logitiles/HEXBERRY-V-20Q100-0.9/HEXBERRY-V-20Q100.kicad_sch

## KiCad design HEXBERRY-V-20Q100.kicad_sch (2024-11-13)

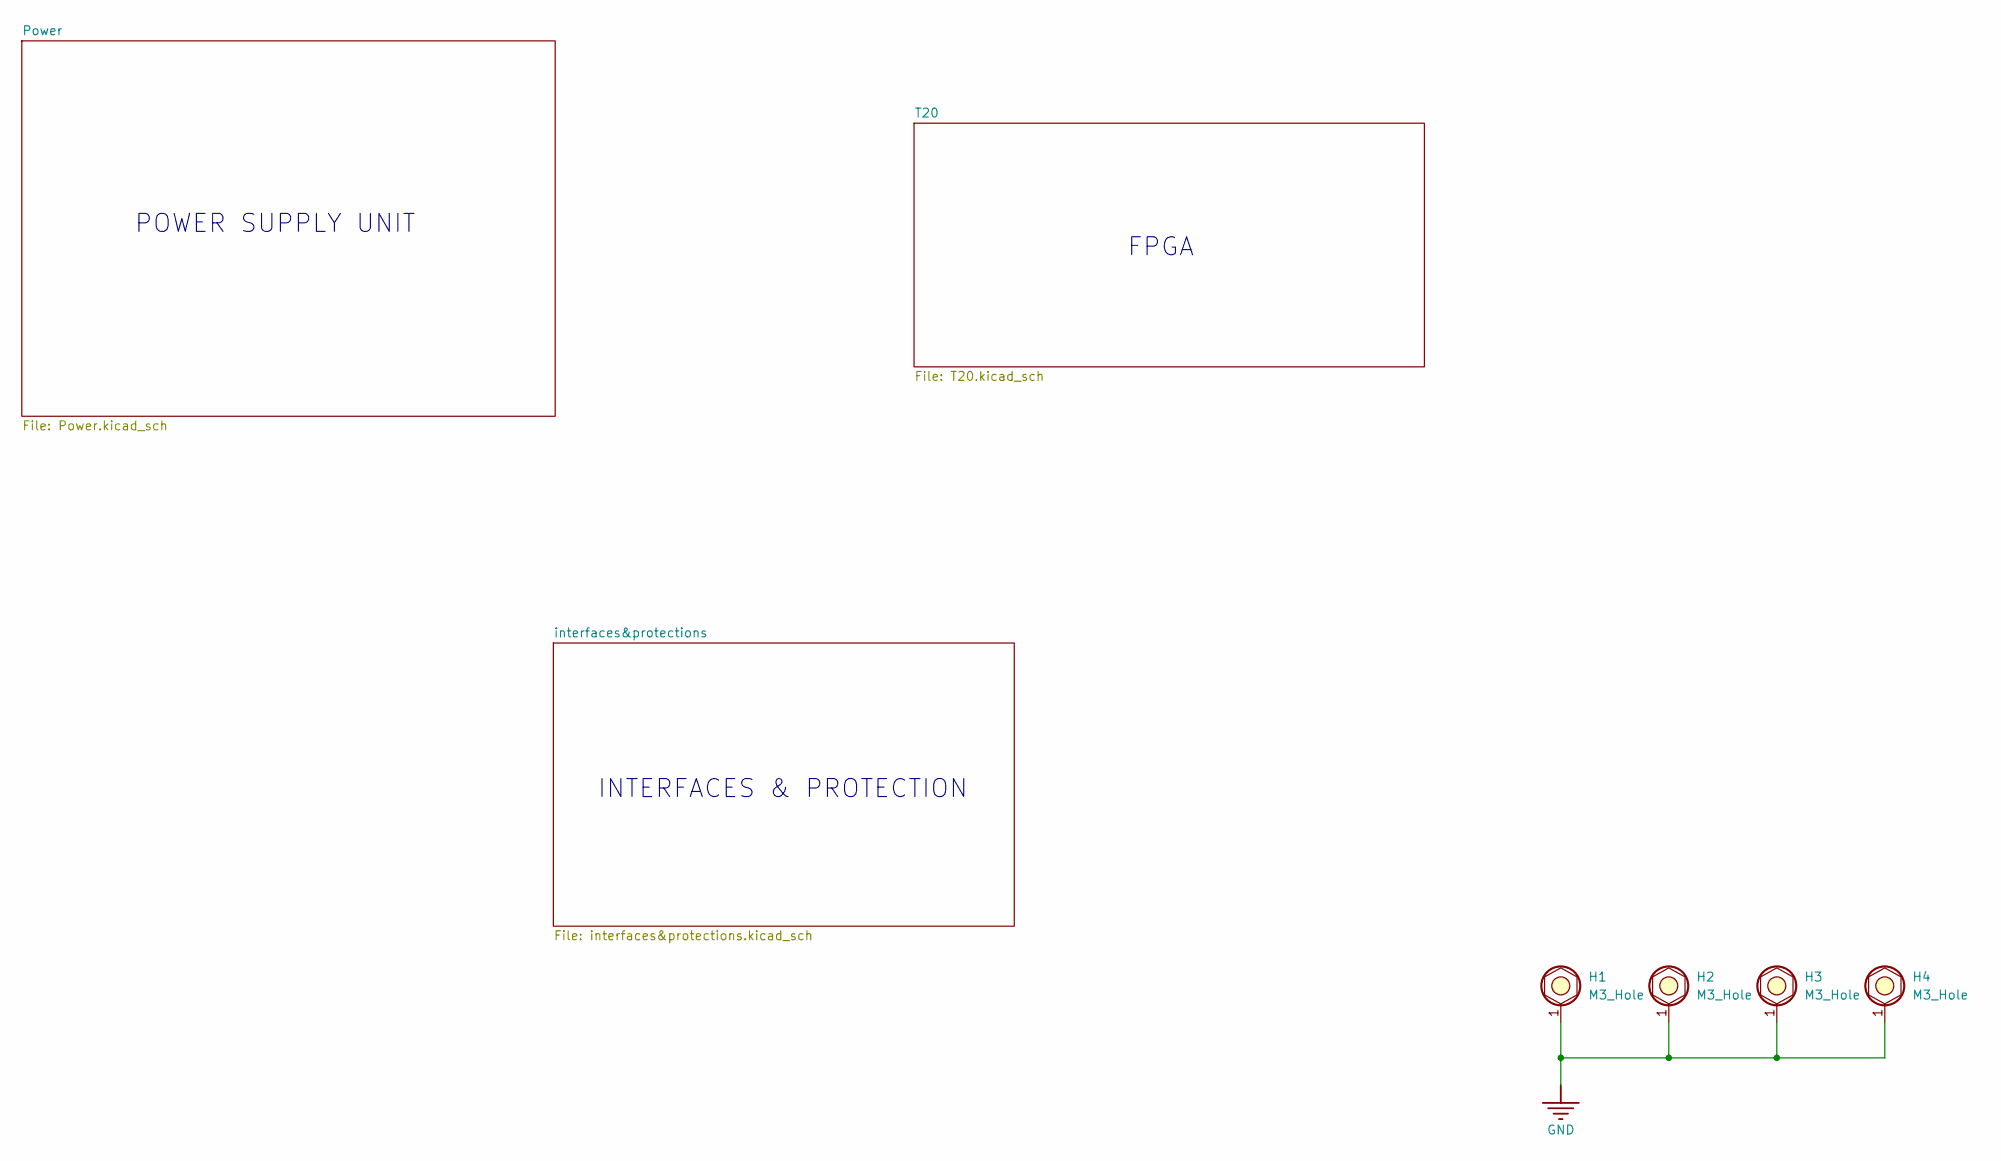
[picture p10: schematic HEXBERRY-V-20Q100.kicad_sch]

Parts:
H1, H2, H3, H4: M3_Hole; MountingHole_3.2mm_With_Spacer_H10mm

Connections:
GND: H1.1, H2.1, H3.1, H4.1

Notes on the sheet:
INTERFACES & PROTECTION
FPGA
POWER SUPPLY UNIT
