logitiles/HEXBERRY-V-20Q100-0.9/Power.kicad_sch

## KiCad design Power.kicad_sch (2024-11-13)

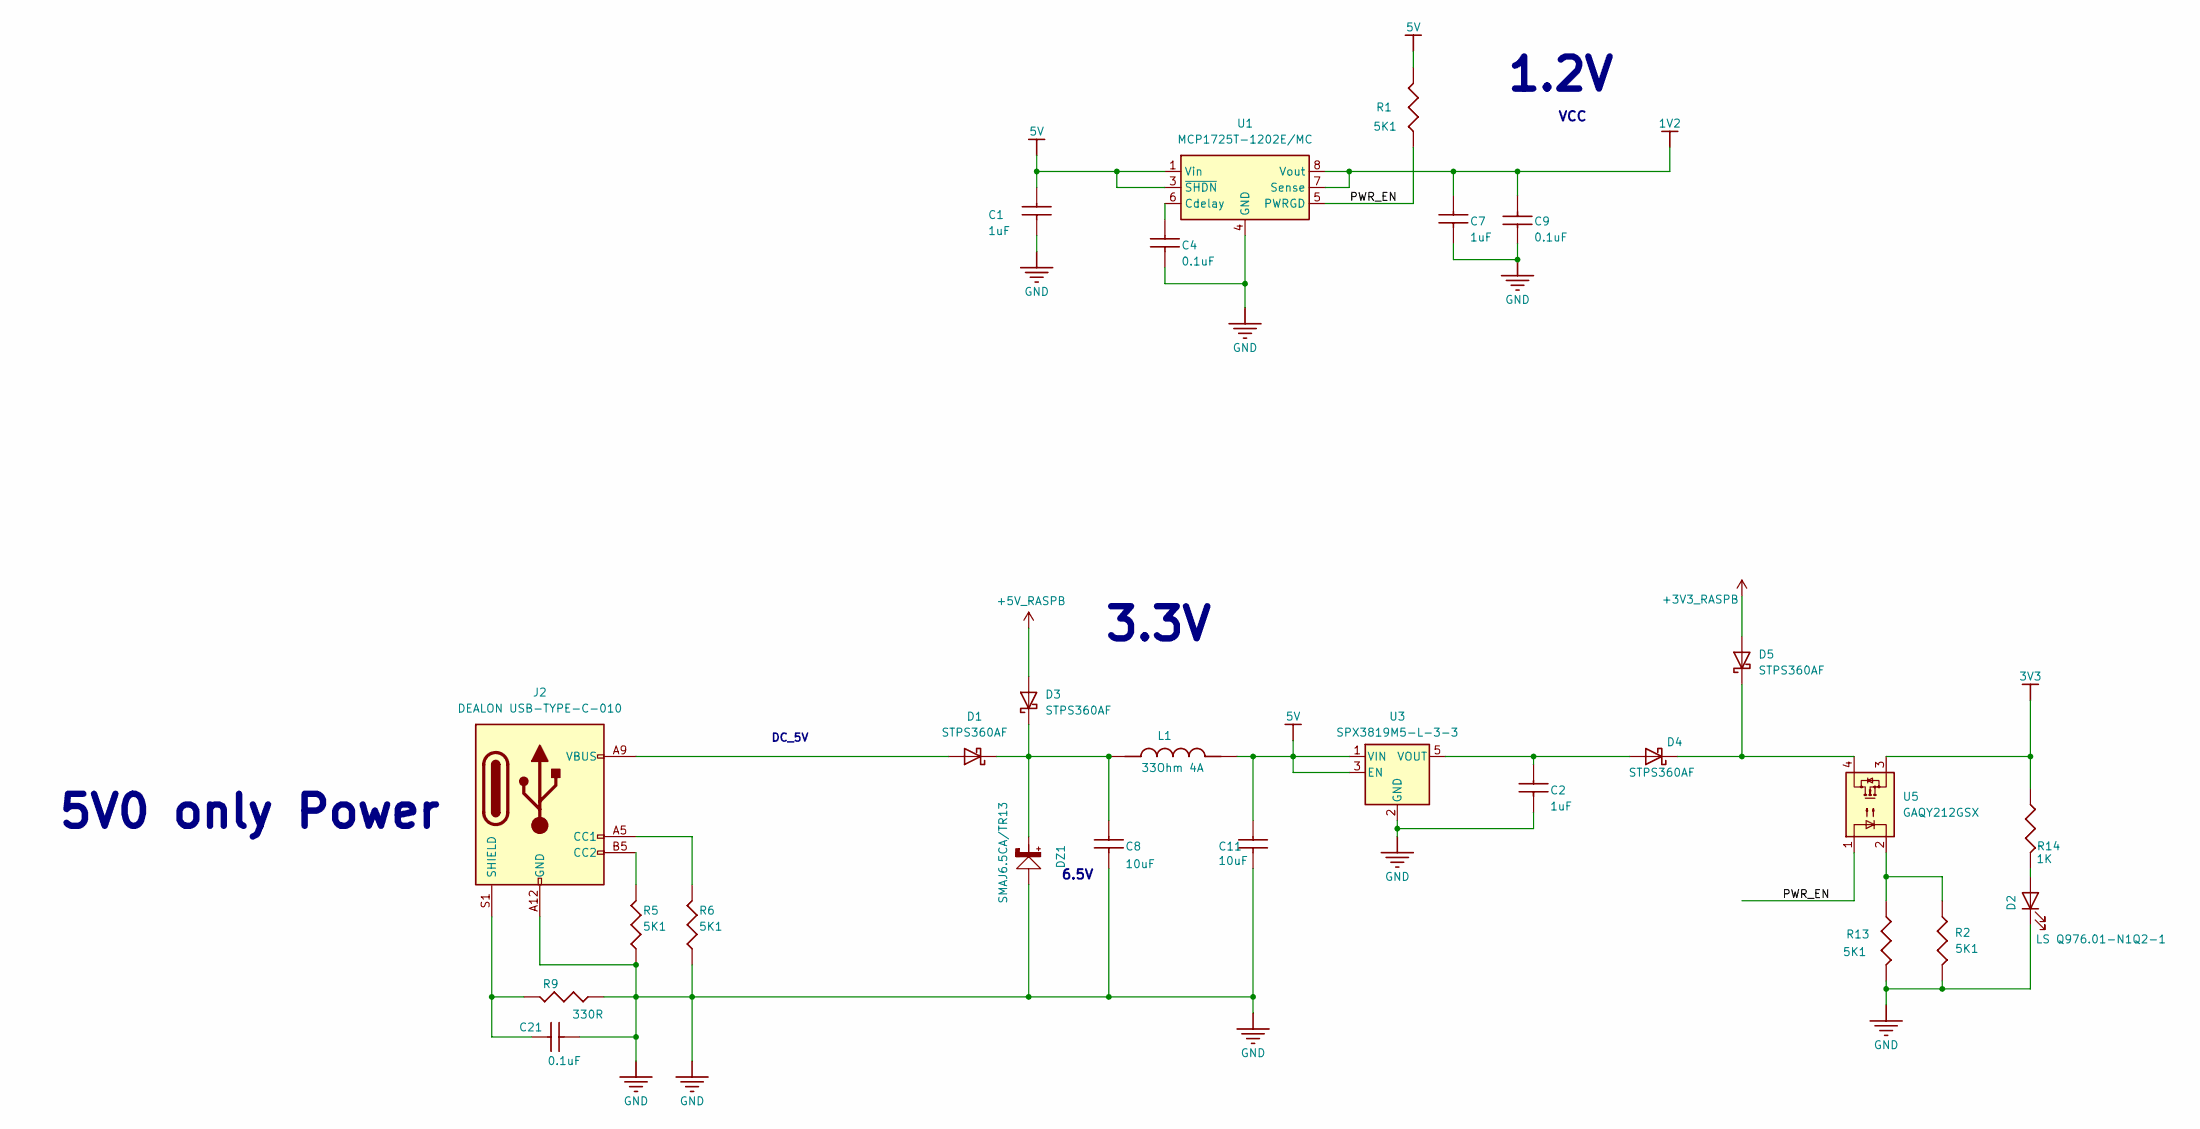
[picture p11: schematic Power.kicad_sch]

Parts:
C1, C2, C7: 1uF; C_0402_1005Metric
C4, C9, C21: 0.1uF; C_0402_1005Metric
C8, C11: 10uF; C_0603_1608Metric
D1, D3, D4, D5: STPS360AF; D_SOD-128
D2: LS Q976.01-N1Q2-1; LED_0603_1608Metric
DZ1: SMAJ6.5CA/TR13; D_SMA
J2: DEALON USB-TYPE-C-010; USB_C_Receptacle_GCT_USB4125-xx-x-0190_6P_TopMnt_Horizontal
L1: 33Ohm 4A; L_0603_1608Metric
R1, R2, R5, R6, R13: 5K1; R_0402_1005Metric
R9: 330R; R_0402_1005Metric
R14: 1K; R_0402_1005Metric
U1: MCP1725T-1202E/MC; DFN-8-1EP_3x3mm_P0.5mm_EP1.65x2.38mm_ThermalVias
U3: SPX3819M5-L-3-3; SOT-23-5
U5: GAQY212GSX; SOP-4_3.8x4.1mm_P2.54mm

Connections:
1V2: C7.1, C9.2, U1.7 (Sense), U1.8 (Vout)
3V3: R14.1, U5.3
5V: C1.1, C11.1, L1.1, R1.2, U1.1 (Vin), U1.2 (Vin), U1.3 (~SHDN), U3.1 (VIN), U3.3 (EN)
+3V3_RASPB: D5.2 (A)
+5V_RASPB: D3.2 (A)
GND: C1.2, C2.2, C4.2, C7.2, C8.2, C9.1, C11.2, C21.2, D2.1 (K), DZ1.1 (A), J2.A12 (GND), J2.B12 (GND), R2.2, R5.1, R6.1, R9.1, R13.2, U1.4 (GND), U1.9 (GND), U3.2 (GND)
unnamed: C2.1, D4.2 (A), U3.5 (VOUT)
unnamed: C4.1, U1.6 (Cdelay)
unnamed: C8.1, D1.1 (K), D3.1 (K), DZ1.2 (K), L1.2
unnamed: C21.1, J2.S1 (SHIELD), R9.2
unnamed: D1.2 (A), J2.A9 (VBUS), J2.B9 (VBUS)
unnamed: D2.2 (A), R14.2
unnamed: D4.1 (K), D5.1 (K), U5.4
unnamed: J2.A5 (CC1), R6.2
unnamed: J2.B5 (CC2), R5.2
unnamed: R2.1, R13.1, U5.2
PWR_EN: R1.1, U1.5 (PWRGD), U5.1

Notes on the sheet:
6.5V
DC_5V
3.3V
1.2V
5V0 only Power
VCC
