logitiles/HEXBERRY-V-20Q100-0.9/T20.kicad_sch

## KiCad design T20.kicad_sch (2024-11-13)

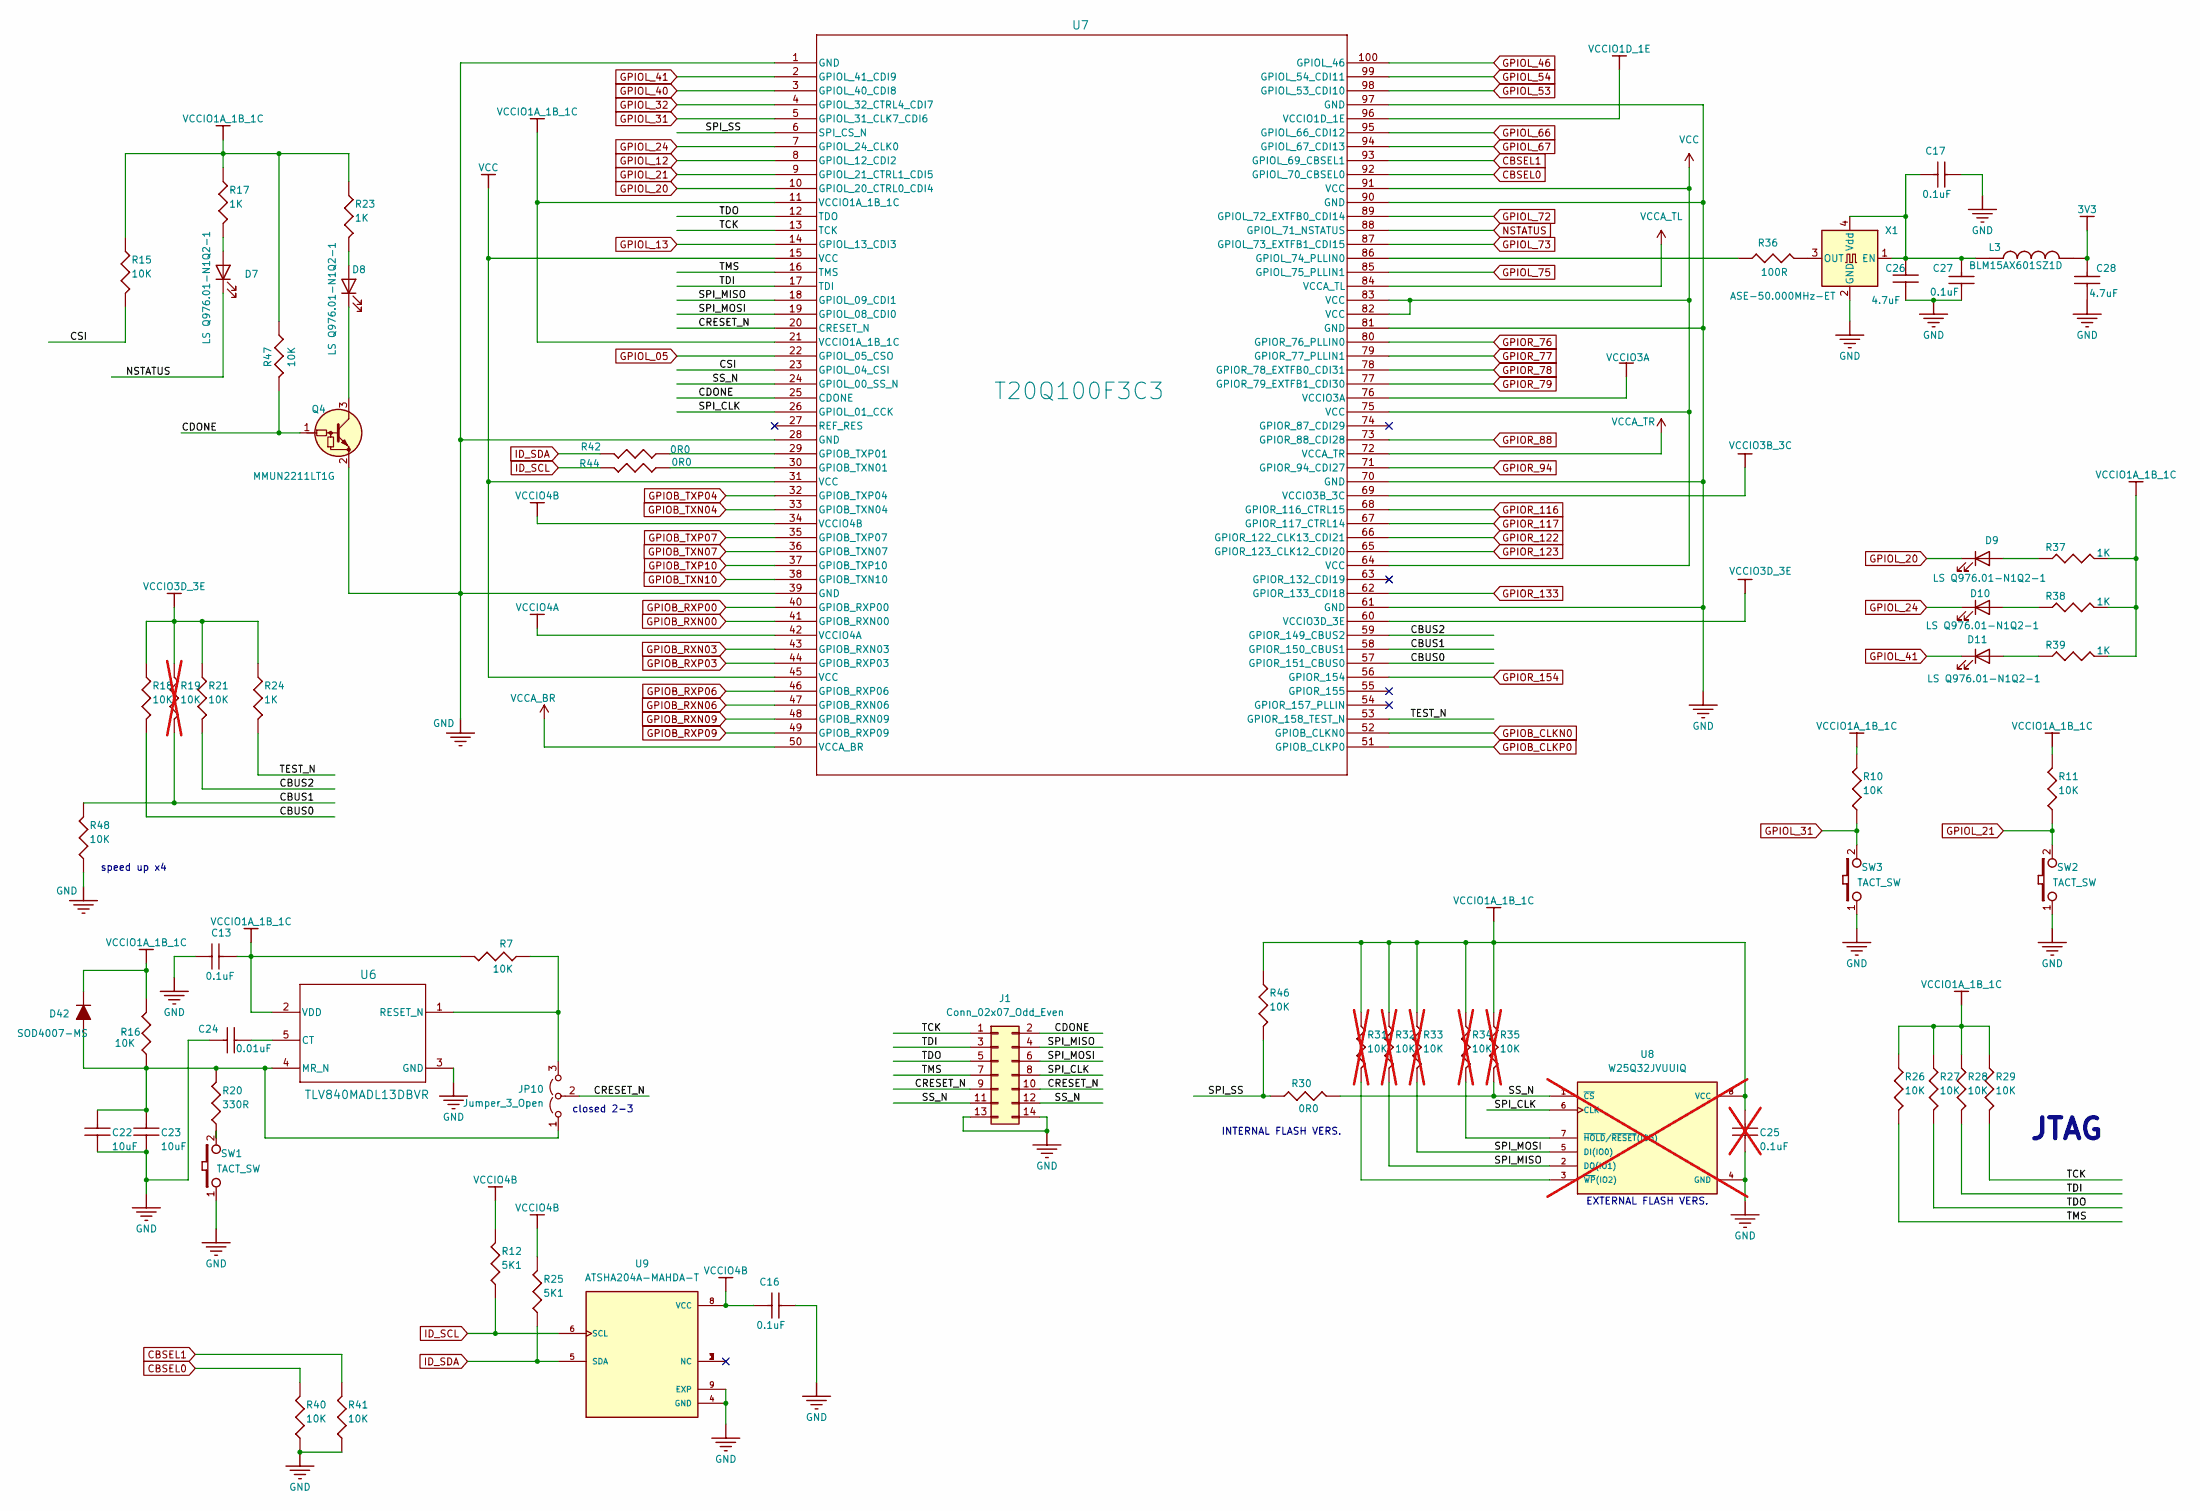
[picture p12: schematic T20.kicad_sch]

Parts:
C13, C16, C17, C27: 0.1uF; C_0402_1005Metric
C22, C23: 10uF; C_0603_1608Metric
C24: 0.01uF; C_0402_1005Metric
C25: 0.1uF; C_0402_1005Metric; not fitted
C26, C28: 4.7uF; C_0402_1005Metric
D7, D8, D9, D10, D11: LS Q976.01-N1Q2-1; LED_0603_1608Metric
D42: SOD4007-MS; D_SOD-123F
J1: Conn_02x07_Odd_Even; PinSocket_2x07_P2.54mm_Vertical
JP10: Jumper_3_Open; SolderJumper-3_P1.3mm_Open_Pad1.0x1.5mm_NumberLabels
L3: BLM15AX601SZ1D; L_0402_1005Metric
Q4: MMUN2211LT1G; SOT-23
R7, R10, R11, R15, R16, R18, R21, R26, R27, R28, R29, R40, R41, R46, R47, R48: 10K; R_0402_1005Metric
R12, R25: 5K1; R_0402_1005Metric
R17, R23, R24, R37, R38, R39: 1K; R_0402_1005Metric
R19, R31, R32, R33, R34, R35: 10K; R_0402_1005Metric; not fitted
R20: 330R; R_0402_1005Metric
R30, R42, R44: 0R0; R_0402_1005Metric
R36: 100R; R_0402_1005Metric
SW1, SW2, SW3: TACT_SW; SW_SPST_B3U-1000P
U6: TLV840MADL13DBVR; SOT-23-5
U7: T20Q100F3C3; LQFP-100_14x14mm_P0.5mm
U8: W25Q32JVUUIQ; WSON-8-1EP_6x5mm_P1.27mm_EP3.4x4mm; not fitted
U9: ATSHA204A-MAHDA-T; TDFN-8-1EP_3x2mm_P0.5mm_EP1.4x1.4mm; PART_REV A
X1: ASE-50.000MHz-ET; Oscillator_SMD_Abracon_ASE-4Pin_3.2x2.5mm

Connections:
3V3: C28.2, L3.1
CBSEL0: R40.2, U7.92 (GPIOL_70_CBSEL0)
CBSEL1: R41.2, U7.93 (GPIOL_69_CBSEL1)
CBUS0: R18.2, U7.57 (GPIOR_151_CBUS0)
CBUS1: R19.2, R48.2, U7.58 (GPIOR_150_CBUS1)
CBUS2: R21.2, U7.59 (GPIOR_149_CBUS2)
CDONE: J1.2, Q4.1 (B), R47.2, U7.25 (CDONE)
CRESET_N: J1.9, J1.10, JP10.2 (C), U7.20 (CRESET_N)
CSI: R15.2, U7.23 (GPIOL_04_CSI)
GND: C13.1, C16.1, C17.1, C22.1, C23.1, C24.2, C25.1, C26.2, C27.1, C28.1, J1.13, J1.14, Q4.2 (E), R40.1, R41.1, R48.1, SW1.1, SW2.1, SW3.1, U6.3 (GND), U7.1 (GND), U7.28 (GND), U7.39 (GND), U7.61 (GND), U7.70 (GND), U7.81 (GND), U7.90 (GND), U7.97 (GND), U8.4 (GND), U9.4 (GND), U9.9 (EXP), X1.2 (GND)
GPIOB_CLKN0: U7.52 (GPIOB_CLKN0)
GPIOB_CLKP0: U7.51 (GPIOB_CLKP0)
GPIOB_RXN00: U7.41 (GPIOB_RXN00)
GPIOB_RXN03: U7.43 (GPIOB_RXN03)
GPIOB_RXN06: U7.47 (GPIOB_RXN06)
GPIOB_RXN09: U7.48 (GPIOB_RXN09)
GPIOB_RXP00: U7.40 (GPIOB_RXP00)
GPIOB_RXP03: U7.44 (GPIOB_RXP03)
GPIOB_RXP06: U7.46 (GPIOB_RXP06)
GPIOB_RXP09: U7.49 (GPIOB_RXP09)
GPIOB_TXN04: U7.33 (GPIOB_TXN04)
GPIOB_TXN07: U7.36 (GPIOB_TXN07)
GPIOB_TXN10: U7.38 (GPIOB_TXN10)
GPIOB_TXP04: U7.32 (GPIOB_TXP04)
GPIOB_TXP07: U7.35 (GPIOB_TXP07)
GPIOB_TXP10: U7.37 (GPIOB_TXP10)
GPIOL_05: U7.22 (GPIOL_05_CSO)
GPIOL_12: U7.8 (GPIOL_12_CDI2)
GPIOL_13: U7.14 (GPIOL_13_CDI3)
GPIOL_20: D9.1 (K), U7.10 (GPIOL_20_CTRL0_CDI4)
GPIOL_21: R11.1, SW2.2, U7.9 (GPIOL_21_CTRL1_CDI5)
GPIOL_24: D10.1 (K), U7.7 (GPIOL_24_CLK0)
GPIOL_31: R10.1, SW3.2, U7.5 (GPIOL_31_CLK7_CDI6)
GPIOL_32: U7.4 (GPIOL_32_CTRL4_CDI7)
GPIOL_40: U7.3 (GPIOL_40_CDI8)
GPIOL_41: D11.1 (K), U7.2 (GPIOL_41_CDI9)
GPIOL_46: U7.100 (GPIOL_46)
GPIOL_53: U7.98 (GPIOL_53_CDI10)
GPIOL_54: U7.99 (GPIOL_54_CDI11)
GPIOL_66: U7.95 (GPIOL_66_CDI12)
GPIOL_67: U7.94 (GPIOL_67_CDI13)
GPIOL_72: U7.89 (GPIOL_72_EXTFB0_CDI14)
GPIOL_73: U7.87 (GPIOL_73_EXTFB1_CDI15)
GPIOL_75: U7.85 (GPIOL_75_PLLIN1)
GPIOR_76: U7.80 (GPIOR_76_PLLIN0)
GPIOR_77: U7.79 (GPIOR_77_PLLIN1)
GPIOR_78: U7.78 (GPIOR_78_EXTFB0_CDI31)
GPIOR_79: U7.77 (GPIOR_79_EXTFB1_CDI30)
GPIOR_88: U7.73 (GPIOR_88_CDI28)
GPIOR_94: U7.71 (GPIOR_94_CDI27)
GPIOR_116: U7.68 (GPIOR_116_CTRL15)
GPIOR_117: U7.67 (GPIOR_117_CTRL14)
GPIOR_122: U7.66 (GPIOR_122_CLK13_CDI21)
GPIOR_123: U7.65 (GPIOR_123_CLK12_CDI20)
GPIOR_133: U7.62 (GPIOR_133_CDI18)
GPIOR_154: U7.56 (GPIOR_154)
ID_SCL: R12.1, R44.2, U9.6 (SCL)
ID_SDA: R25.1, R42.2, U9.5 (SDA)
NSTATUS: D7.1 (K), U7.88 (GPIOL_71_NSTATUS)
unnamed: C17.2, C26.1, C27.2, L3.2, X1.1 (EN), X1.4 (Vdd)
unnamed: C22.2, C23.2, D42.2 (A), JP10.1 (A), R16.1, R20.2, U6.4 (MR_N)
unnamed: C24.1, U6.5 (CT)
unnamed: D7.2 (A), R17.2
unnamed: D8.1 (K), Q4.3 (C)
unnamed: D8.2 (A), R23.2
unnamed: D9.2 (A), R37.1
unnamed: D10.2 (A), R38.1
unnamed: D11.2 (A), R39.1
unnamed: JP10.3 (B), R7.1, U6.1 (RESET_N)
unnamed: R20.1, SW1.2
unnamed: R31.2, U8.3 (~WP(IO2))
unnamed: R34.2, U8.7 (~HOLD/~RESET(IO3))
unnamed: R36.1, U7.86 (GPIOL_74_PLLIN0)
unnamed: R36.2, X1.3 (OUT)
unnamed: R42.1, U7.29 (GPIOB_TXP01)
unnamed: R44.1, U7.30 (GPIOB_TXN01)
unnamed: U9.1 (NC), U9.2 (NC), U9.3 (NC), U9.7 (NC)
SPI_CLK: J1.8, U7.26 (GPIOL_01_CCK), U8.6 (CLK)
SPI_MISO: J1.4, R32.2, U7.18 (GPIOL_09_CDI1), U8.2 (DO(IO1))
SPI_MOSI: J1.6, R33.2, U7.19 (GPIOL_08_CDI0), U8.5 (DI(IO0))
SPI_SS: R30.1, R46.2, U7.6 (SPI_CS_N)
SS_N: J1.11, J1.12, R30.2, R35.2, U7.24 (GPIOL_00_SS_N), U8.1 (~CS)
TCK: J1.1, R29.2, U7.13 (TCK)
TDI: J1.3, R28.2, U7.17 (TDI)
TDO: J1.5, R27.2, U7.12 (TDO)
TEST_N: R24.2, U7.53 (GPIOR_158_TEST_N)
TMS: J1.7, R26.2, U7.16 (TMS)
VCC: U7.15 (VCC), U7.31 (VCC), U7.45 (VCC), U7.64 (VCC), U7.75 (VCC), U7.82 (VCC), U7.83 (VCC), U7.91 (VCC)
VCCA_BR: U7.50 (VCCA_BR)
VCCA_TL: U7.84 (VCCA_TL)
VCCA_TR: U7.72 (VCCA_TR)
VCCIO1A_1B_1C: C13.2, C25.2, D42.1 (K), R7.2, R10.2, R11.2, R15.1, R16.2, R17.1, R23.1, R26.1, R27.1, R28.1, R29.1, R31.1, R32.1, R33.1, R34.1, R35.1, R37.2, R38.2, R39.2, R46.1, R47.1, U6.2 (VDD), U7.11 (VCCIO1A_1B_1C), U7.21 (VCCIO1A_1B_1C), U8.8 (VCC)
VCCIO1D_1E: U7.96 (VCCIO1D_1E)
VCCIO3A: U7.76 (VCCIO3A)
VCCIO3B_3C: U7.69 (VCCIO3B_3C)
VCCIO3D_3E: R18.1, R19.1, R21.1, R24.1, U7.60 (VCCIO3D_3E)
VCCIO4A: U7.42 (VCCIO4A)
VCCIO4B: C16.2, R12.2, R25.2, U7.34 (VCCIO4B), U9.8 (VCC)

Notes on the sheet:
closed 2-3
speed up x4
EXTERNAL FLASH VERS.
JTAG
INTERNAL FLASH VERS.
