logitiles/HEXBERRY-V-20Q100-0.9/interfaces&protections.kicad_sch

## KiCad design interfaces&protections.kicad_sch (2024-11-13)

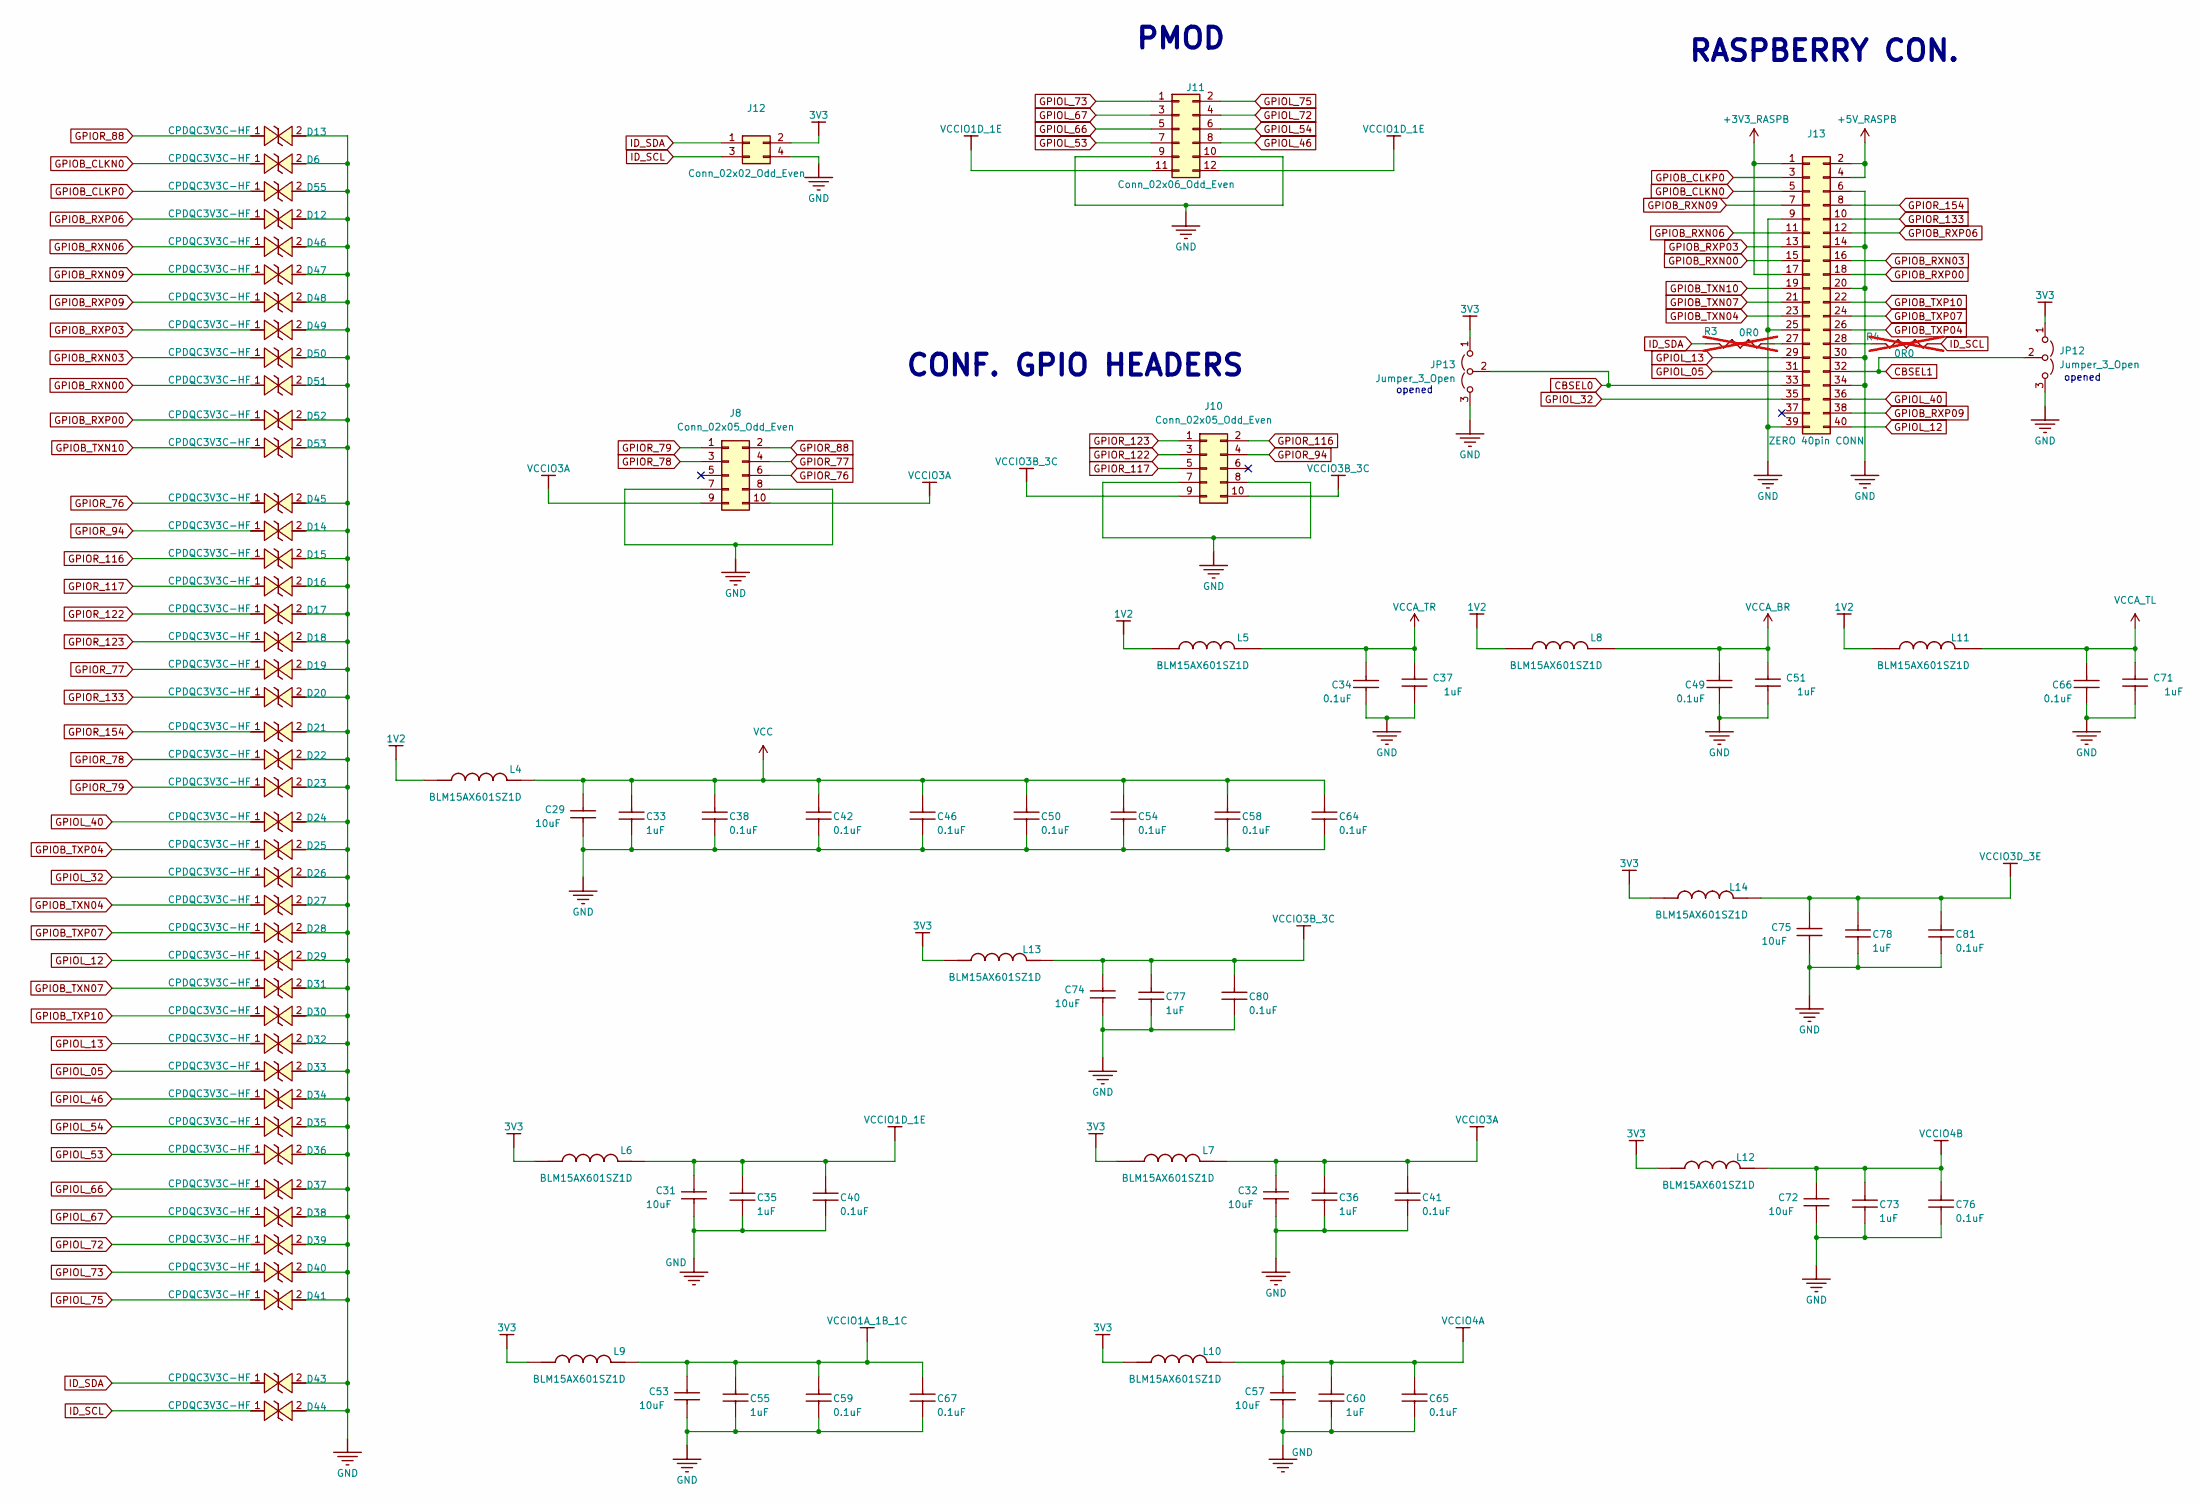
[picture p13: schematic interfaces&protections.kicad_sch]

Parts:
C29, C31, C32, C53, C57, C72, C74, C75: 10uF; C_0603_1608Metric
C33, C35, C36, C37, C51, C55, C60, C71, C73, C77, C78: 1uF; C_0402_1005Metric
C34, C38, C40, C41, C42, C46, C49, C50, C54, C58, C59, C64, C65, C66, C67, C76, C80, C81: 0.1uF; C_0402_1005Metric
D6, D12, D13, D14, D15, D16, D17, D18, D19, D20, D21, D22, D23, D24, D25, D26, D27, D28, D29, D30, D31, D32, D33, D34, D35, D36, D37, D38, D39, D40, D41, D43, D44, D45, D46, D47, D48, D49, D50, D51, D52, D53, D55: CPDQC3V3C-HF; D_0402_1005Metric
J8, J10: Conn_02x05_Odd_Even; PinSocket_2x05_P2.54mm_Vertical
J11: Conn_02x06_Odd_Even; PinSocket_2x06_P2.54mm_Vertical
J12: Conn_02x02_Odd_Even; PinHeader_2x02_P2.54mm_Vertical
J13: ZERO 40pin CONN; PinSocket_2x20_P2.54mm_Vertical
JP12, JP13: Jumper_3_Open; SolderJumper-3_P1.3mm_Open_Pad1.0x1.5mm_NumberLabels
L4, L5, L6, L7, L8, L9, L10, L11, L12, L13, L14: BLM15AX601SZ1D; L_0402_1005Metric
R3, R4: 0R0; R_0402_1005Metric; not fitted

Connections:
1V2: L4.1, L5.1, L8.1, L11.1
3V3: J12.2, JP12.1 (A), JP13.1 (A), L6.1, L7.1, L9.1, L10.1, L12.1, L13.1, L14.1
+3V3_RASPB: J13.1, J13.17
+5V_RASPB: J13.2, J13.4
CBSEL0: J13.33, JP13.2 (C)
CBSEL1: J13.32, JP12.2 (C)
GND: C29.2, C31.2, C32.2, C33.1, C34.1, C35.1, C36.1, C37.2, C38.1, C40.1, C41.1, C42.1, C46.1, C49.1, C50.1, C51.2, C53.2, C54.1, C55.1, C57.2, C58.1, C59.1, C60.1, C64.1, C65.1, C66.1, C67.1, C71.2, C72.2, C73.1, C74.2, C75.2, C76.1, C77.1, C78.1, C80.1, C81.1, D6.2 (C), D12.2 (C), D13.2 (C), D14.2 (C), D15.2 (C), D16.2 (C), D17.2 (C), D18.2 (C), D19.2 (C), D20.2 (C), D21.2 (C), D22.2 (C), D23.2 (C), D24.2 (C), D25.2 (C), D26.2 (C), D27.2 (C), D28.2 (C), D29.2 (C), D30.2 (C), D31.2 (C), D32.2 (C), D33.2 (C), D34.2 (C), D35.2 (C), D36.2 (C), D37.2 (C), D38.2 (C), D39.2 (C), D40.2 (C), D41.2 (C), D43.2 (C), D44.2 (C), D45.2 (C), D46.2 (C), D47.2 (C), D48.2 (C), D49.2 (C), D50.2 (C), D51.2 (C), D52.2 (C), D53.2 (C), D55.2 (C), J8.7, J8.8, J10.7, J10.8, J11.9, J11.10, J12.4, J13.6, J13.9, J13.14, J13.20, J13.25, J13.30, J13.34, J13.39, JP12.3 (B), JP13.3 (B)
GPIOB_CLKN0: D6.1 (A), J13.5
GPIOB_CLKP0: D55.1 (A), J13.3
GPIOB_RXN00: D51.1 (A), J13.15
GPIOB_RXN03: D50.1 (A), J13.16
GPIOB_RXN06: D46.1 (A), J13.11
GPIOB_RXN09: D47.1 (A), J13.7
GPIOB_RXP00: D52.1 (A), J13.18
GPIOB_RXP03: D49.1 (A), J13.13
GPIOB_RXP06: D12.1 (A), J13.12
GPIOB_RXP09: D48.1 (A), J13.38
GPIOB_TXN04: D27.1 (A), J13.23
GPIOB_TXN07: D31.1 (A), J13.21
GPIOB_TXN10: D53.1 (A), J13.19
GPIOB_TXP04: D25.1 (A), J13.26
GPIOB_TXP07: D28.1 (A), J13.24
GPIOB_TXP10: D30.1 (A), J13.22
GPIOL_05: D33.1 (A), J13.31
GPIOL_12: D29.1 (A), J13.40
GPIOL_13: D32.1 (A), J13.29
GPIOL_32: D26.1 (A), J13.35
GPIOL_40: D24.1 (A), J13.36
GPIOL_46: D34.1 (A), J11.8
GPIOL_53: D36.1 (A), J11.7
GPIOL_54: D35.1 (A), J11.6
GPIOL_66: D37.1 (A), J11.5
GPIOL_67: D38.1 (A), J11.3
GPIOL_72: D39.1 (A), J11.4
GPIOL_73: D40.1 (A), J11.1
GPIOL_75: D41.1 (A), J11.2
GPIOR_76: D45.1 (A), J8.6
GPIOR_77: D19.1 (A), J8.4
GPIOR_78: D22.1 (A), J8.3
GPIOR_79: D23.1 (A), J8.1
GPIOR_88: D13.1 (A), J8.2
GPIOR_94: D14.1 (A), J10.4
GPIOR_116: D15.1 (A), J10.2
GPIOR_117: D16.1 (A), J10.5
GPIOR_122: D17.1 (A), J10.3
GPIOR_123: D18.1 (A), J10.1
GPIOR_133: D20.1 (A), J13.10
GPIOR_154: D21.1 (A), J13.8
ID_SCL: D44.1 (A), J12.3, R4.1
ID_SDA: D43.1 (A), J12.1, R3.2
unnamed: J13.27, R3.1
unnamed: J13.28, R4.2
VCC: C29.1, C33.2, C38.2, C42.2, C46.2, C50.2, C54.2, C58.2, C64.2, L4.2
VCCA_BR: C49.2, C51.1, L8.2
VCCA_TL: C66.2, C71.1, L11.2
VCCA_TR: C34.2, C37.1, L5.2
VCCIO1A_1B_1C: C53.1, C55.2, C59.2, C67.2, L9.2
VCCIO1D_1E: C31.1, C35.2, C40.2, J11.11, J11.12, L6.2
VCCIO3A: C32.1, C36.2, C41.2, J8.9, J8.10, L7.2
VCCIO3B_3C: C74.1, C77.2, C80.2, J10.9, J10.10, L13.2
VCCIO3D_3E: C75.1, C78.2, C81.2, L14.2
VCCIO4A: C57.1, C60.2, C65.2, L10.2
VCCIO4B: C72.1, C73.2, C76.2, L12.2

Notes on the sheet:
PMOD
CONF. GPIO HEADERS
opened
RASPBERRY CON.
